const-meg/Offendoor/despieceversionfinal.PNG

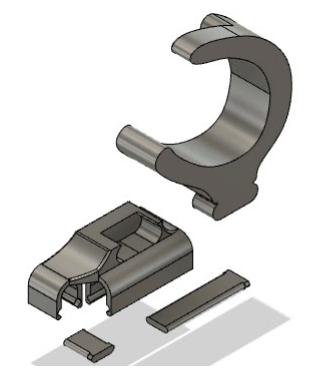
despieceversionfinal.PNG
