const-meg/Offendoor/impresionbase.PNG

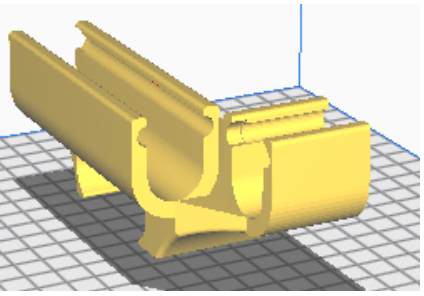
impresionbase.PNG
