const-meg/Offendoor/impresiontapas.PNG

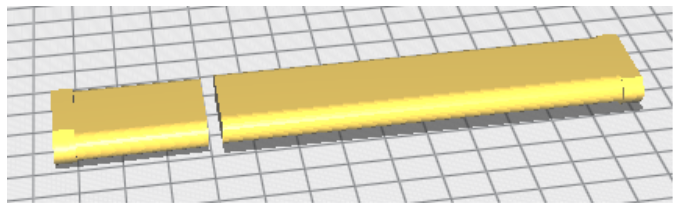
impresiontapas.PNG
