const-meg/Offendoor/versionfinal.PNG

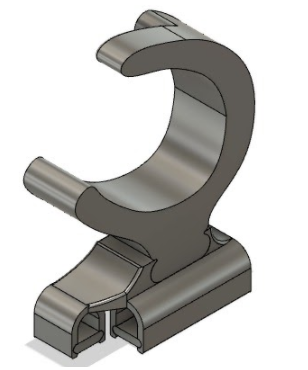
versionfinal.PNG
